CDonohoe-Designs/STM32WL-LoRa-Sensor-Board-Portfolio/Hardware/STM32WL_BlockDiagram.pdf

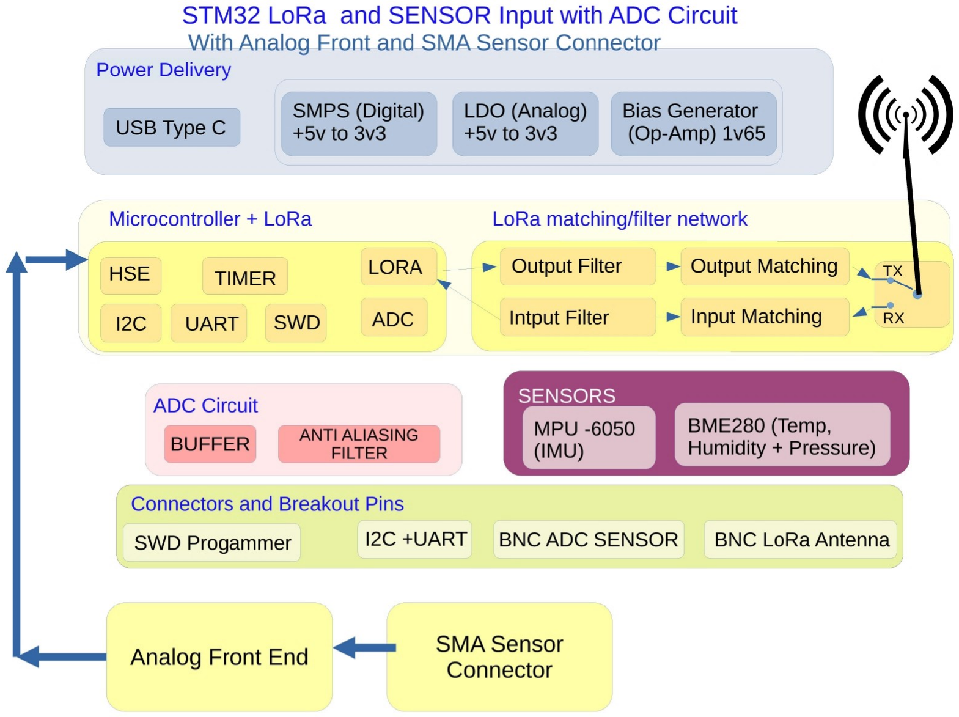
[picture p39: page 1]
