CDonohoe-Designs/STM32WL-LoRa-Sensor-Board-Portfolio/Images/Layer2_GND.JPG

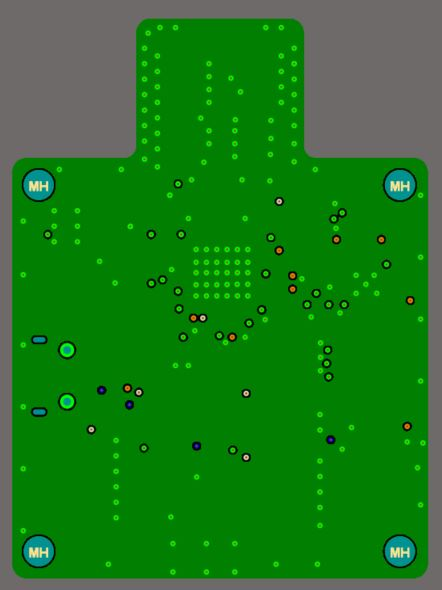
Images/Layer2_GND.JPG
