CDonohoe-Designs/STM32WL-LoRa-Sensor-Board-Portfolio/Images/Layer3_+3V3.JPG

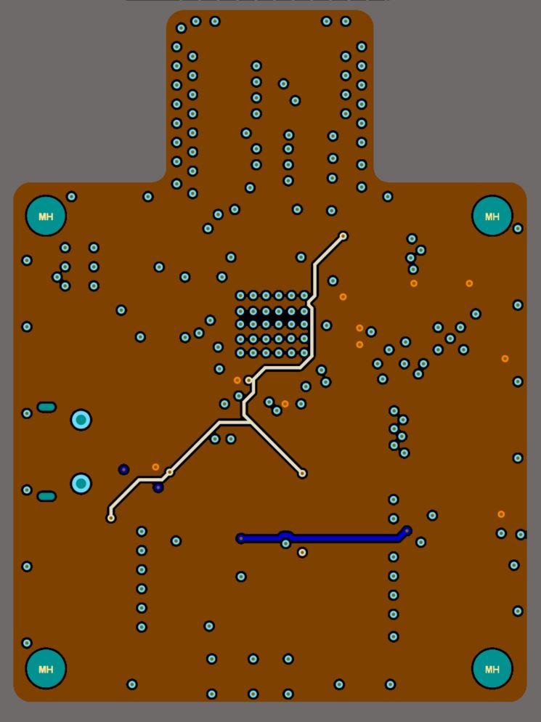
Images/Layer3_+3V3.JPG
