CDonohoe-Designs/STM32WL-LoRa-Sensor-Board-Portfolio/Images/STM32WL_DRC.jpg

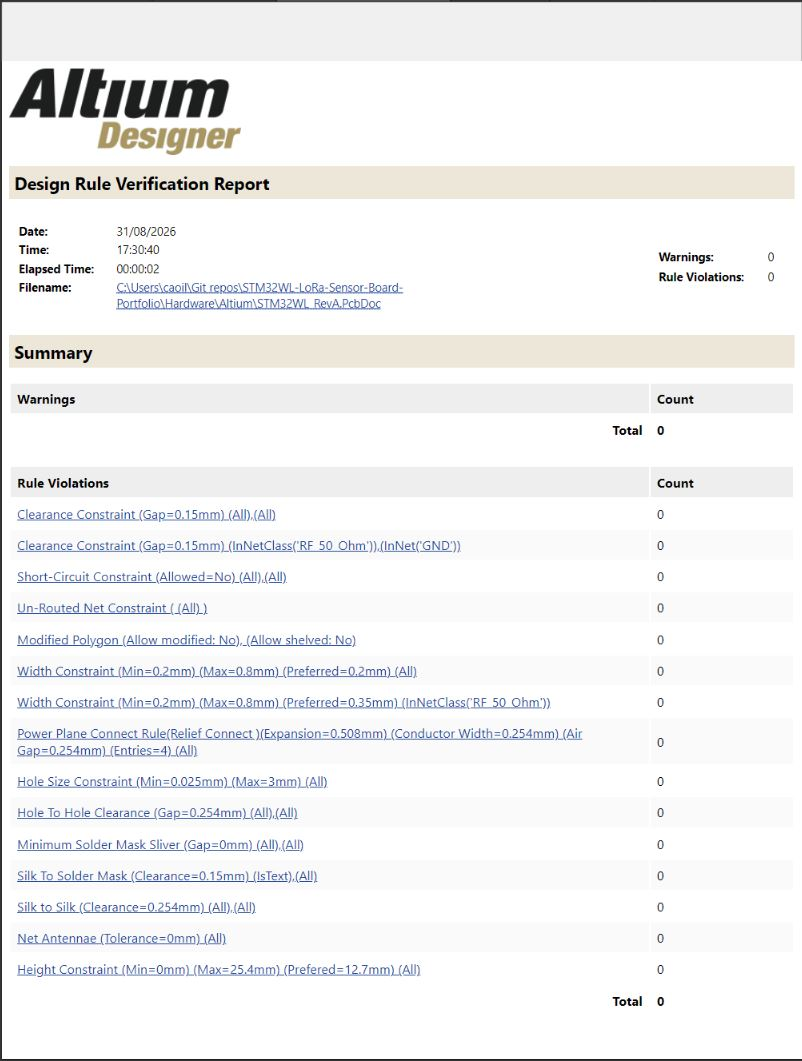
Images/STM32WL_DRC.jpg
