CDonohoe-Designs/STM32WL-LoRa-Sensor-Board-Portfolio/Images/STM32WL_PCB.jpg

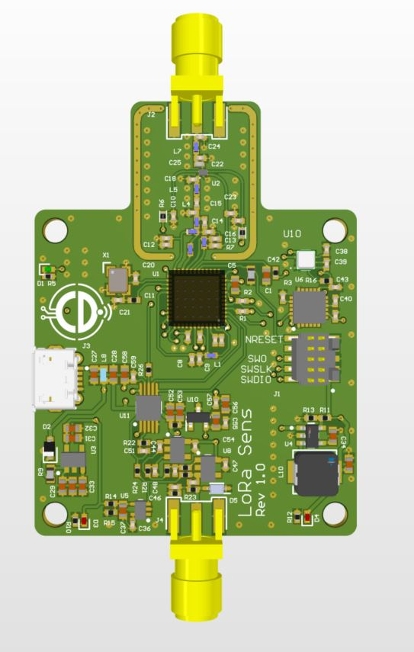
Images/STM32WL_PCB.jpg
