CDonohoe-Designs/STM32WL-LoRa-Sensor-Board-Portfolio/Images/STM32WL_PCB_3D.jpg

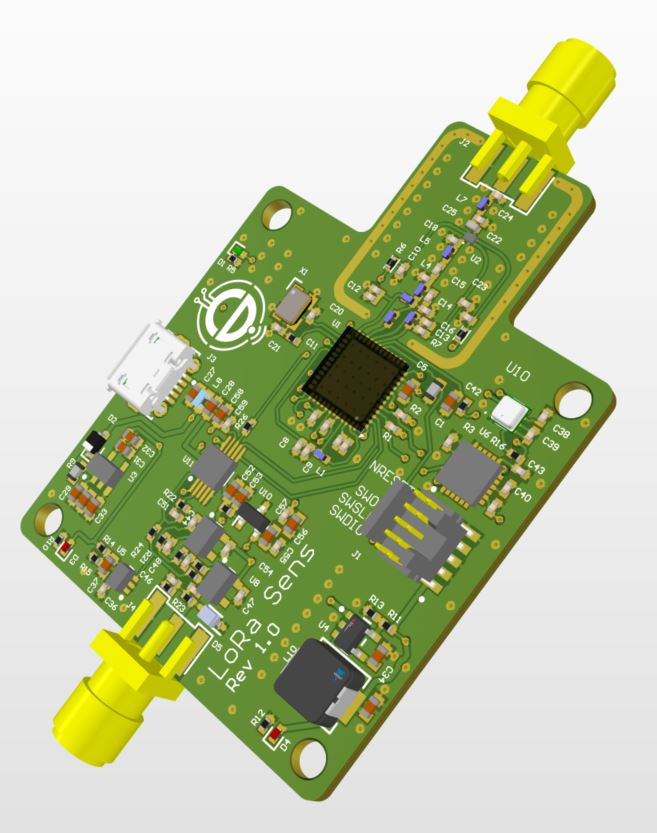
Images/STM32WL_PCB_3D.jpg
